equinoxorg/standalone_v2/Software/standalone/interrupted_charging.c

#include "interrupted_charging.h"
#include "ui.h"
#include "rtc.h"

void calc_lvdc ( float );
void set_temperature_compensation( float, float*, float* );
void set_current_compensation ( float, float, float* );

#define BULK_CHARGING			1
#define VOLTAGE_SETTLE		2
#define PULSED_CURRENT		3
#define FULLY_CHARGED			4
#define NIGHT_MODE 				5

float v_high = 14.7f;
float v_low = 13.4f;
float v_restart = 12.8f;
float v_lvdc = 11.8f;				//If adjusting, also need to modify calc_lvdc() function
float pulse_duty = 0.33f;

float batt_voltage = 0.0f, batt_current = 0.0f;
float temp;

//Choosen based on the consumption of running 
//CC circuitry
#define P_NIGHT_MODE 0.7f

//Private Variables
int cc_state = NIGHT_MODE;

//Public Variables
U64 interrupted_charging_stk[I_CHARGING_STK_SIZE];
OS_TID interrupted_charging_t;

__task void interrupted_charging (void)
{
	float sol_voltage = 0.0f, sol_current = 0.0f, sol_power = 0.0f;
	int pulse = 0;
	int counter = 0;
	
	//TODO: initialise hardware
	init_pwm(40000);
	init_adc();
	
	set_mppt();
		
	while (1)
	{
		batt_voltage = get_adc_voltage(ADC_BATT_V);
		batt_current = get_adc_voltage(ADC_BATT_I);
		sol_voltage = get_adc_voltage(ADC_SOL_V);
		sol_current = get_adc_voltage(ADC_SOL_I);
		sol_power = sol_voltage * sol_current;
		temp = get_adc_voltage(ADC_TEMP);
		
		set_temperature_compensation( temp, &v_high, &pulse_duty );
		
		TRACE_INFO("1,%.0f,%i,%.2f,%.2f,%.2f,%.3f,%.1f,%.2F\n",
					((double)get_time_t()), cc_state, batt_voltage, batt_current, sol_voltage, sol_current, duty_cycle, temp);
		
		//Check for LVDC voltage
		calc_lvdc(batt_current);
		if ( batt_voltage < v_lvdc )
		{
			//Turn off outputs and screen.
			//send os event to turn off
			os_evt_set( UI_LVDC, ui_t );
		}	
		
		switch (cc_state)
		{
			case BULK_CHARGING:
				//Start charging battery with 0.1C current or as high as possible if 0.1C cannot be met
				perturb_and_observe_cc_itter(BATTERY_AHR*0.1f);
				
				if (++counter > 10)
					set_current_compensation(BATTERY_AHR*0.1f, batt_current, &v_high);
			
				if (sol_power < P_NIGHT_MODE)
				{
					if (set_mppt() < (P_NIGHT_MODE*1.2))
					{
						cc_state = NIGHT_MODE;
						counter = 0;
						TRACE_DEBUG("Starting Night Mode State\n");
						break;
					}
					TRACE_DEBUG("Rescaned Power and Night mode not entered \n");
				}
		
						
				if (batt_voltage > v_high)
				{
					cc_state = VOLTAGE_SETTLE;
					counter = 0;
					TRACE_DEBUG("Starting Voltage Settle Charging State at V=%f \n", batt_voltage);
					break;
				}
				
				os_dly_wait( P_AND_O_PERIOD );

				break;
			
			case VOLTAGE_SETTLE:
				//Diable the MPPT Charging Circuit
				GPIO_ResetBits(GPIOB, GPIO_Pin_0);
			
				if (batt_voltage < v_low)
				{
					GPIO_SetBits(GPIOB, GPIO_Pin_0);
					cc_state = PULSED_CURRENT;
					TRACE_DEBUG("Starting Pulsed Current Charging State at V=%f \n", batt_voltage);
					break;
				}				
				//5s delay
				os_dly_wait(50);
				break;
				
			case PULSED_CURRENT:
				counter++;

				if (pulse)
				{
					//If greater than high period seconds, pulse is low. i.e sets up x% duty cycle
					if ( counter > (300 * pulse_duty) )
						pulse = 0;
					
					//Enable MPPT hardware
					GPIO_SetBits(GPIOB, GPIO_Pin_0);
					
					//Run p&o itteration
					perturb_and_observe_cc_itter(BATTERY_AHR*0.05f);
					
					
					if ( counter > 10 )
						{
						//set_current_compensation(BATTERY_AHR*0.05f, batt_current);
							
						if (sol_power < P_NIGHT_MODE)
						{
							if (set_mppt() < (P_NIGHT_MODE*1.2))
							{
								cc_state = NIGHT_MODE;
								counter = 0;
								TRACE_DEBUG("Starting Night Mode State\n");
								break;
							}
							TRACE_DEBUG("Rescaned Power and Night mode not entered \n");
						}
					}
				}
				else
				{
					//If greater than 30s, reset.
					if ( counter > 300)
					{
						counter = 0;
						pulse = 1;
					}
					//Diable the MPPT Charging Circuit
					GPIO_ResetBits(GPIOB, GPIO_Pin_0);
				}
				
								
				if (batt_voltage > v_high)
				{
					counter = 0;
					cc_state = FULLY_CHARGED;
					TRACE_DEBUG("Starting Fully Charged Charging State at V=%f \n", batt_voltage);
					break;
				}
				
				//100ms delay
				os_dly_wait(10);				
				break;
			case FULLY_CHARGED:
				//Regulate so that Battery current = 0
					//This means that the battery is no longer charged
					//But the panel is used to power any connected load
			
				//Diable the MPPT Charging Circuit
				GPIO_ResetBits(GPIOB, GPIO_Pin_0);				
			
				//Check when to start recharging again.
				if (batt_voltage < v_restart)
				{
					cc_state = BULK_CHARGING;
					TRACE_DEBUG("Restarting the Bulk Charging State \n");
					break;
				}
			
				//5s delay
				os_dly_wait(500);
				break;
			
			case NIGHT_MODE:
				//Check every 5 minutes
				//Counter used so that LVDC is still
				//checked every 5 seconds
				if (++counter > 2)
				{
					//Enable MPPT Circuit
					GPIO_SetBits(GPIOB, GPIO_Pin_0);
				
					if (set_mppt() > (P_NIGHT_MODE*1.2)) 
					{
						cc_state = BULK_CHARGING;
						TRACE_DEBUG("Exiting Night Mode\n");
						break;
					}
					
					//Diable the MPPT Charging Circuit
					//GPIO_ResetBits(GPIOB, GPIO_Pin_0);
					set_duty_cycle(100);
					
					counter = 0;
				}
				
				//5 second wait time
				os_dly_wait(500);			
				
				break;
			default:
				cc_state = BULK_CHARGING;
				TRACE_ERROR("Charging State machine entered Unknown State. Restarting with Bulk Charging \n");
		}
	}
}

void calc_lvdc ( float current )
{
	if ( current < (-5.0f * BATTERY_AHR) )
		v_lvdc = 9.6f;
	else if ( current < (-0.1f * BATTERY_AHR) )
		v_lvdc = ( (current / BATTERY_AHR) * (2.2f / 4.9f) ) + 11.8449f;
	else
		v_lvdc = 11.8f;
}


//For explainations of these compensation values please read project report.
void set_temperature_compensation( float temp, float* voltage, float* duty_cycle )
{
	if ( temp < 5 )
	{
		*voltage = 14.7;
		*duty_cycle = 0.167f;
	}
	else if ( temp < 25 )
	{
		*voltage = 14.7;
		*duty_cycle = (0.00815f * temp) + 0.1265f;
	}
	else if ( temp < 50 )
	{
		*voltage = 16.2f - (0.06f * temp);
		*duty_cycle = 0.33f;
	}
	else
	{
		*voltage = 13.2;
		*duty_cycle = 0.33f;
	}
}

void set_current_compensation (float target_current, float measured_current, float* voltage)
{
	//Circular buffer for averaging current ratio
	const int array_size = 4;
	static float current_ratio_array [array_size];
	static int index = 0;
	
	float current_ratio = 0;
	int i;

	current_ratio_array[index] = measured_current / target_current;
	
	
	for (i=0; i<array_size; i++)
	{
		current_ratio += current_ratio_array[i];
	}
	
	current_ratio = current_ratio / array_size;
		
			
	if ( current_ratio < 0.25f)
		*voltage = *voltage * 0.897959184f;
	else
		*voltage = *voltage * ( (2*current_ratio + 12.7f) / 14.7f);
}

float get_charging_rate (void)
{
	if (cc_state == BULK_CHARGING)
		return batt_current / 0.1f;
	else if (cc_state == PULSED_CURRENT)
		return batt_current / 0.05f;
	else if (cc_state == VOLTAGE_SETTLE)
		return 1.0f;
	else
		return 0.0f;
}

int get_soc (void)
{
	float upper_voltage = 14.7f;
	float duty_cycle;
	
	if (cc_state == FULLY_CHARGED)
		return 100;
	else if (cc_state == PULSED_CURRENT)
		return 90;
	else if (cc_state == VOLTAGE_SETTLE)
		return 80;
	else
	{
		batt_voltage = get_adc_voltage(ADC_BATT_V);
		set_temperature_compensation( get_adc_voltage(ADC_TEMP), &upper_voltage, &duty_cycle );
		set_current_compensation(BATTERY_AHR*0.1f, batt_current, &upper_voltage );
		//Linear appoximation
		return (int)( 80.0f*(batt_voltage - v_lvdc) / (upper_voltage - v_lvdc) );
	}

}
