equinoxorg/standalone_v2/Software/standalone/standalone_config.h

#ifndef __standalone_config_h
#define __standalone_config_h

#include "stm32f0xx.h"
#include <RTL.h>
#include <stdio.h>

//#define DEBUG

#ifdef DEBUG
	#define USE_FULL_ASSERT
	#warning "Using Debug mode, for production do not use debug mode"
	#define TRACE_LEVEL TRACE_LEVEL_DEBUG
#else
	#define TRACE_LEVEL TRACE_LEVEL_INFO
#endif

#include "trace.h"

#define BOX_TYPE	HOME

#if BOX_TYPE == HOME
	#define BATTERY_AHR 	7.0f
	#define PV_PANEL_PEAK	7.0f
#endif

#define CODE_AUTHOR "Ashley Grealish"
#define CODE_AUTHOR_EMAIL "ag5509@ic.ac.uk"

#endif
