equinoxorg/standalone_v2/Software/standalone/adc.h

#ifndef __adc_h
#define __adc_h

#include "standalone_config.h"

#ifndef ADC_VREF
	#define ADC_VREF 3.3f
#endif

#define ADC_SOL_V		ADC_Channel_1 //PA1
#define ADC_SOL_I		ADC_Channel_2 //PA2
#define ADC_BATT_V	ADC_Channel_3 //PA3
#define ADC_BATT_I	ADC_Channel_4 //PA4
#define ADC_TEMP		ADC_Channel_TempSensor


#define SCALE_V_SOL(x)	((x) * ((10.0f + 1.33f) / 1.33f ) )
#define SCALE_I_SOL(x)	( x / (0.004f * 0.1f * 1330.0f) )
#define SCALE_V_BATT(x)	((x) * ((10.0f + 1.33f) / 1.33f ) )
#define SCALE_I_BATT(x) ((x-(ADC_VREF/2)) * (0.01f * 50.0f) )

//Convert a current to an equivilent ADC reading
#define I_BATT_TO_ADC(x)	( (uint16_t) ( ( ((x/(0.01f * 50.f))+(ADC_VREF/2)) / ADC_VREF ) * 0xFFF) )

#define NO_SAMPLES 16
#define NO_CHANNELS 5

//Public Variables
extern volatile uint16_t RegularConvData_Tab[NO_SAMPLES * NO_CHANNELS];
extern OS_TID adc_test_t;


/* Private variables ---------------------------------------------------------*/

/* Public function prototypes -----------------------------------------------*/
void init_adc( void );
float get_adc_voltage (uint32_t);
__task void adc_test (void);

#endif
