equinoxorg/standalone_v2/Software/standalone/user_outputs.c

#include "user_outputs.h"


/**
  * @brief  Configure PA5 and PA6 falling edge in interrupt mode
	*					and PF6 and PF7 as output pins
  * @param  None
  * @retval None
  */
void usb_outputs_init (void)
{
	EXTI_InitTypeDef   EXTI_InitStructure;
  GPIO_InitTypeDef   GPIO_InitStructure;
  NVIC_InitTypeDef   NVIC_InitStructure;
	
	//Set up USB Enable Pins
	
	/* GPIOF Clocks enable */
  RCC_AHBPeriphClockCmd( RCC_AHBPeriph_GPIOF, ENABLE);
  
  /* GPIOF Configuration*/
  GPIO_InitStructure.GPIO_Pin = GPIO_Pin_6 | GPIO_Pin_7;
  GPIO_InitStructure.GPIO_Mode = GPIO_Mode_OUT;
  GPIO_InitStructure.GPIO_Speed = GPIO_Speed_50MHz;
  GPIO_InitStructure.GPIO_OType = GPIO_OType_PP;
  GPIO_InitStructure.GPIO_PuPd = GPIO_PuPd_NOPULL ;
  GPIO_Init(GPIOF, &GPIO_InitStructure);
	
	//Set up USB Error Interrupts
  // GPIOA Clocks enable 
  RCC_AHBPeriphClockCmd( RCC_AHBPeriph_GPIOA, ENABLE);
  
  // GPIOA Configuration
  GPIO_InitStructure.GPIO_Pin = GPIO_Pin_5 | GPIO_Pin_6;
  GPIO_InitStructure.GPIO_Mode = GPIO_Mode_IN;
  GPIO_InitStructure.GPIO_Speed = GPIO_Speed_50MHz;
  GPIO_InitStructure.GPIO_OType = GPIO_OType_PP;
	//Enable Pull-ups on USB Flag Pins
  GPIO_InitStructure.GPIO_PuPd = GPIO_PuPd_UP ;
  GPIO_Init(GPIOA, &GPIO_InitStructure);

  /* Enable SYSCFG clock */
  RCC_APB2PeriphClockCmd(RCC_APB2Periph_SYSCFG, ENABLE);
  
  /* Connect EXTI5 Line to PA5 pin */
  SYSCFG_EXTILineConfig(EXTI_PortSourceGPIOA, EXTI_PinSource5);
	/* Connect EXTI6 Line to PA6 pin */
  SYSCFG_EXTILineConfig(EXTI_PortSourceGPIOA, EXTI_PinSource6);
	
  /* Configure EXTI5 & EXTI6 line */
  EXTI_InitStructure.EXTI_Line = EXTI_Line5 | EXTI_Line6;
  EXTI_InitStructure.EXTI_Mode = EXTI_Mode_Interrupt;
  EXTI_InitStructure.EXTI_Trigger = EXTI_Trigger_Falling;
  EXTI_InitStructure.EXTI_LineCmd = ENABLE;
  EXTI_Init(&EXTI_InitStructure);

  /* Enable and set EXTI4_15 Interrupt */
  NVIC_InitStructure.NVIC_IRQChannel = EXTI4_15_IRQn;
  NVIC_InitStructure.NVIC_IRQChannelPriority = 0x00;
  NVIC_InitStructure.NVIC_IRQChannelCmd = ENABLE;
  NVIC_Init(&NVIC_InitStructure);
}

void dc_outputs_init (void)
{
	GPIO_InitTypeDef GPIO_InitStructure;
	
	/* GPIOF Clocks enable */
  RCC_AHBPeriphClockCmd( RCC_AHBPeriph_GPIOA, ENABLE);
  
  /* GPIOF Configuration*/
  GPIO_InitStructure.GPIO_Pin = GPIO_Pin_12;
  GPIO_InitStructure.GPIO_Mode = GPIO_Mode_OUT;
  GPIO_InitStructure.GPIO_Speed = GPIO_Speed_50MHz;
  GPIO_InitStructure.GPIO_OType = GPIO_OType_PP;
  GPIO_InitStructure.GPIO_PuPd = GPIO_PuPd_NOPULL ;
  GPIO_Init(GPIOA, &GPIO_InitStructure);
  
}
