equinoxorg/standalone_v2/Software/standalone/perturb_and_observe.h

#ifndef __PERTURB_AND_OBSERVE_H
#define __PERTURB_AND_OBSERVE_H

#include "standalone_config.h"

#include "adc.h"
#include "pwm.h"

#define P_AND_O_PERIOD	50 //0.5s
#define DUTY_CYCLE_INC (float)1.0f

__task void perturb_and_observe (void);
void perturb_and_observe_itter (void);
void perturb_and_observe_cc_itter (float);
float set_mppt (void);

//Public variables
extern float duty_cycle;

#endif
